SMDynamicsLab/Tappingduino/manuscript/figures/Asynch_S001_BB_alltrials.png

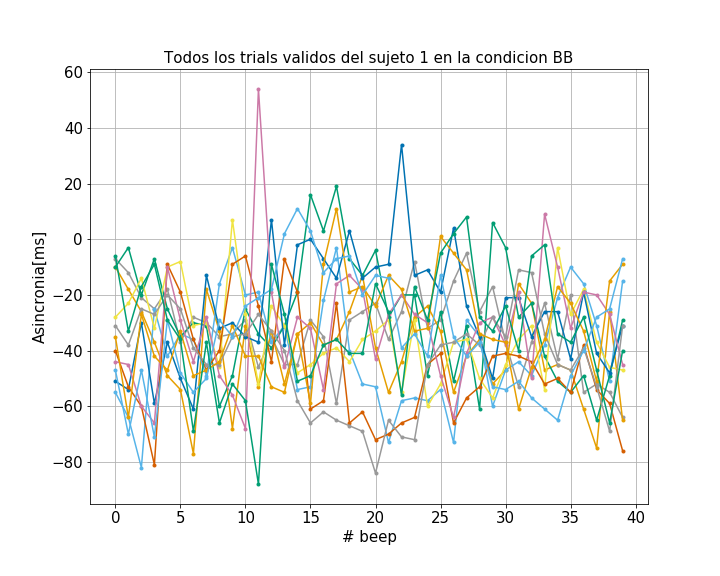
manuscript/figures/Asynch_S001_BB_alltrials.png
