SMDynamicsLab/Tappingduino/manuscript/figures/CuadroANOVA_ID.png

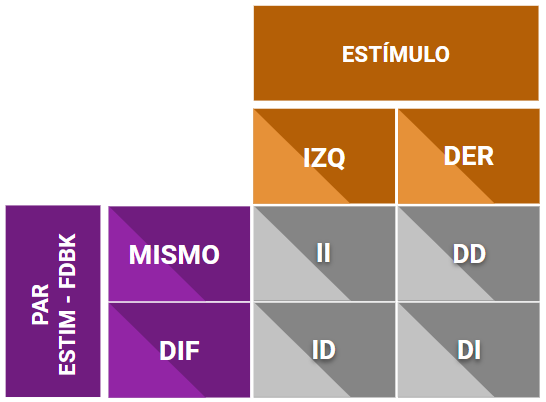
manuscript/figures/CuadroANOVA_ID.png
