SMDynamicsLab/Tappingduino/manuscript/figures/CuadroANOVA_ID_cb.png

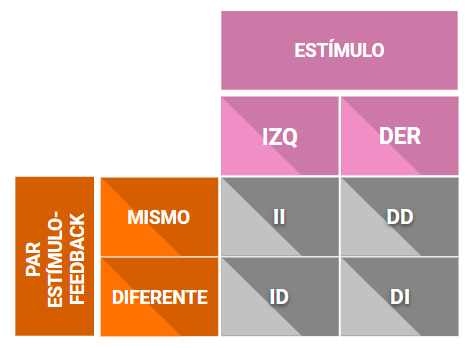
manuscript/figures/CuadroANOVA_ID_cb.png
