SMDynamicsLab/Tappingduino/manuscript/figures/CuadroStimFdbkEsp.png

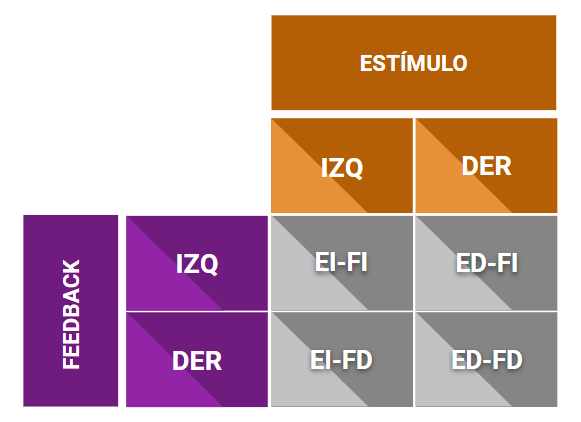
manuscript/figures/CuadroStimFdbkEsp.png
