SMDynamicsLab/Tappingduino/manuscript/figures/distrib_asinc_esquema.png

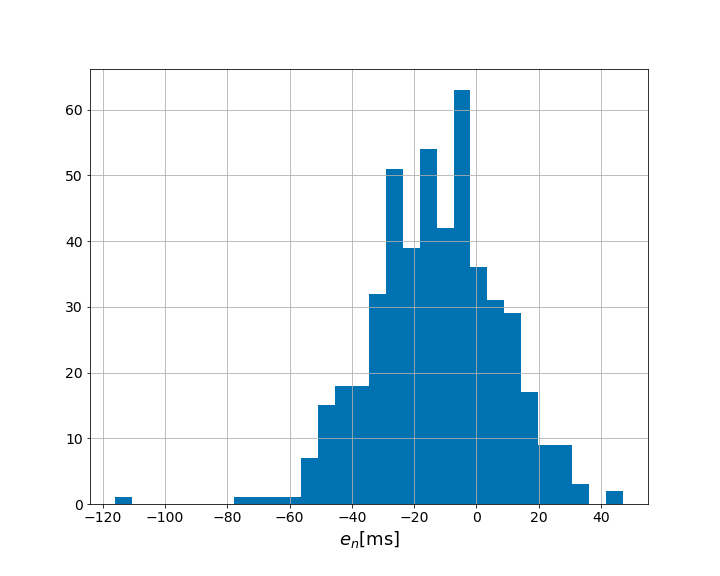
manuscript/figures/distrib_asinc_esquema.png
