SMDynamicsLab/Tappingduino/manuscript/figures/DistribAsinc_CondDD.png

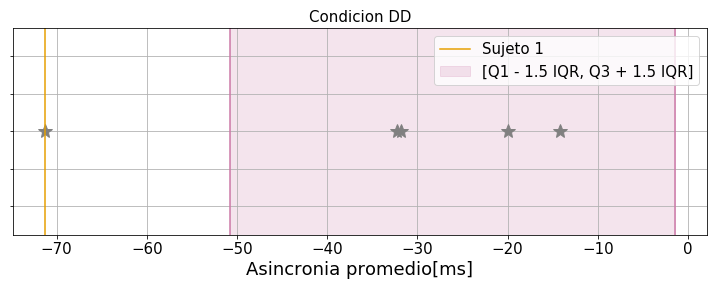
manuscript/figures/DistribAsinc_CondDD.png
