SMDynamicsLab/Tappingduino/manuscript/figures/esquema1av2.png

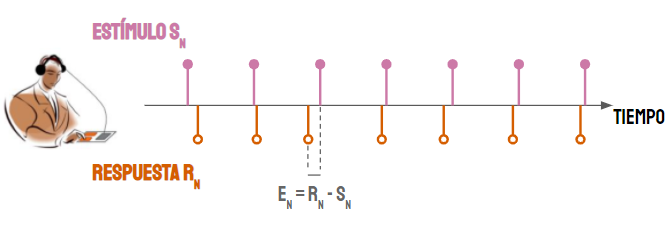
manuscript/figures/esquema1av2.png
