SMDynamicsLab/Tappingduino/manuscript/figures/esquema1b.png

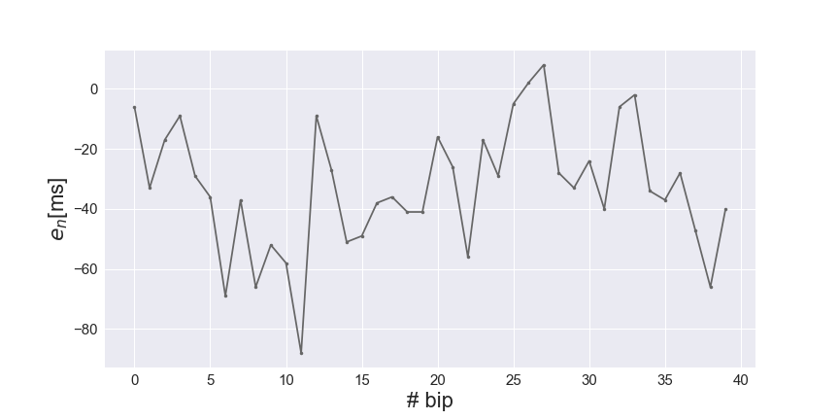
manuscript/figures/esquema1b.png
