SMDynamicsLab/Tappingduino/manuscript/figures/esquema2v2.png

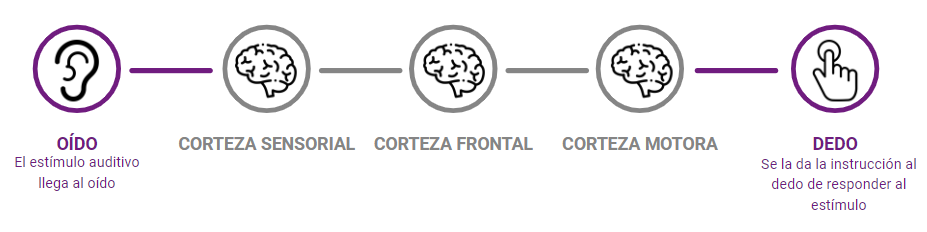
manuscript/figures/esquema2v2.png
