SMDynamicsLab/Tappingduino/manuscript/figures/esquema2v3.png

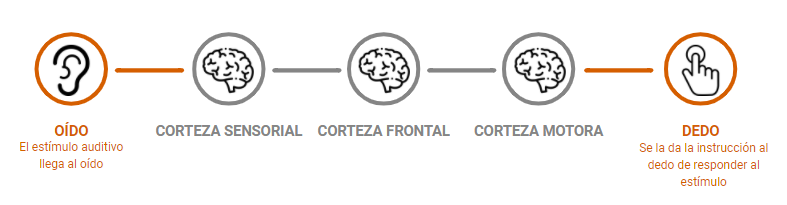
manuscript/figures/esquema2v3.png
