SMDynamicsLab/Tappingduino/manuscript/figures/esquema3v3.png

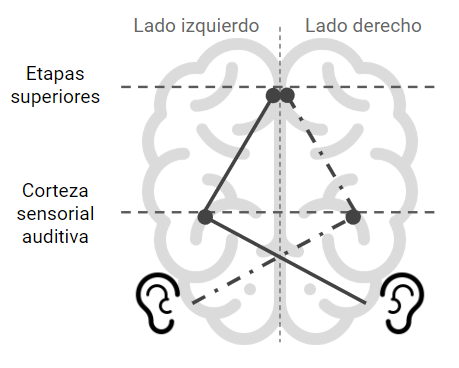
manuscript/figures/esquema3v3.png
