SMDynamicsLab/Tappingduino/manuscript/figures/esquema3v4.png

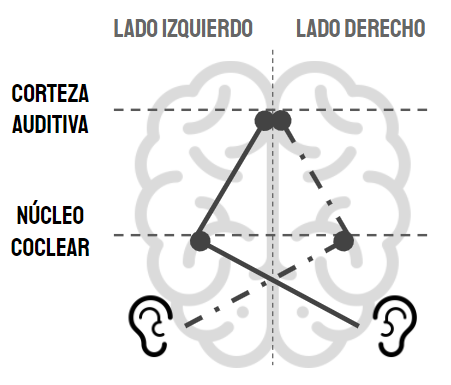
manuscript/figures/esquema3v4.png
