SMDynamicsLab/Tappingduino/manuscript/figures/esquema3v5.png

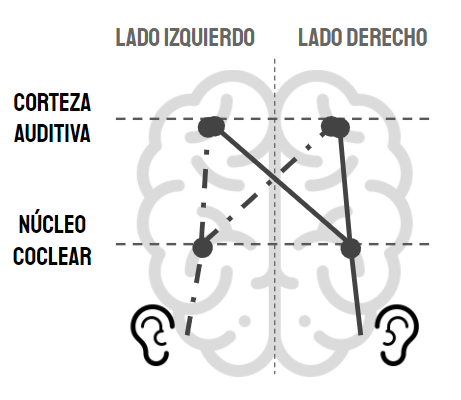
manuscript/figures/esquema3v5.png
