SMDynamicsLab/Tappingduino/manuscript/figures/esquema3v6.png

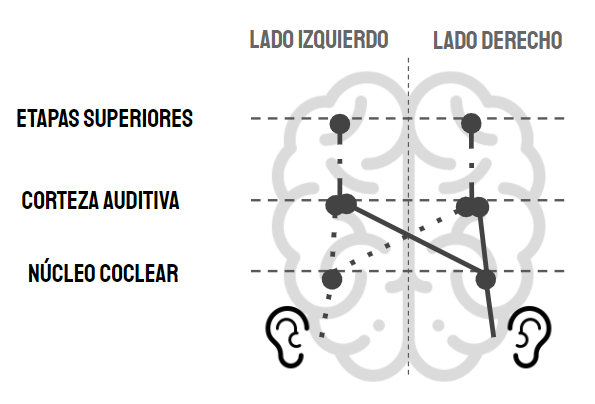
manuscript/figures/esquema3v6.png
