SMDynamicsLab/Tappingduino/manuscript/figures/esquema4av2.png

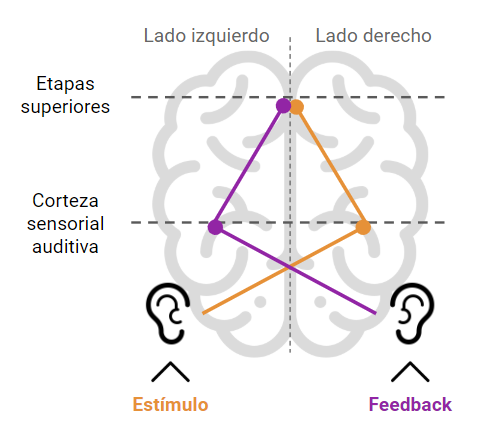
manuscript/figures/esquema4av2.png
