SMDynamicsLab/Tappingduino/manuscript/figures/esquema4bv2.png

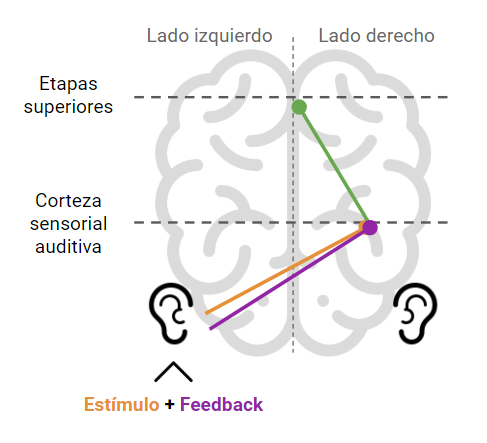
manuscript/figures/esquema4bv2.png
