SMDynamicsLab/Tappingduino/manuscript/figures/esquema4v2.png

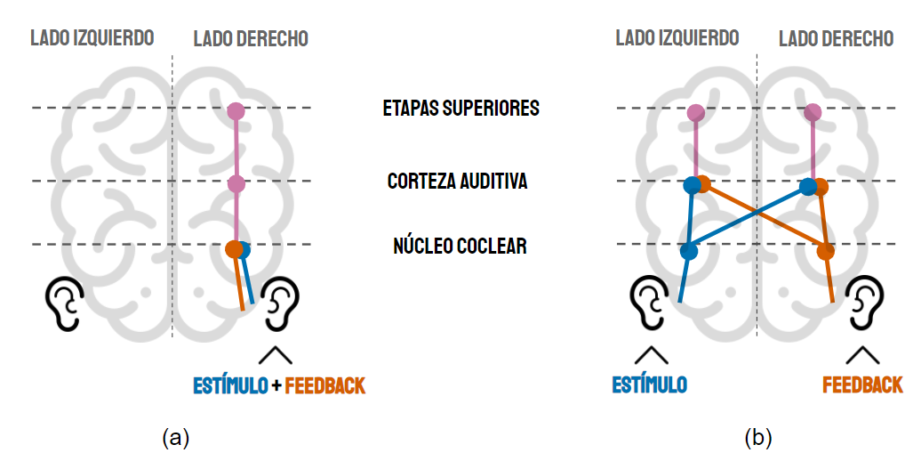
manuscript/figures/esquema4v2.png
