SMDynamicsLab/Tappingduino/manuscript/figures/Factores_nuevos_3subj_MEAN.png

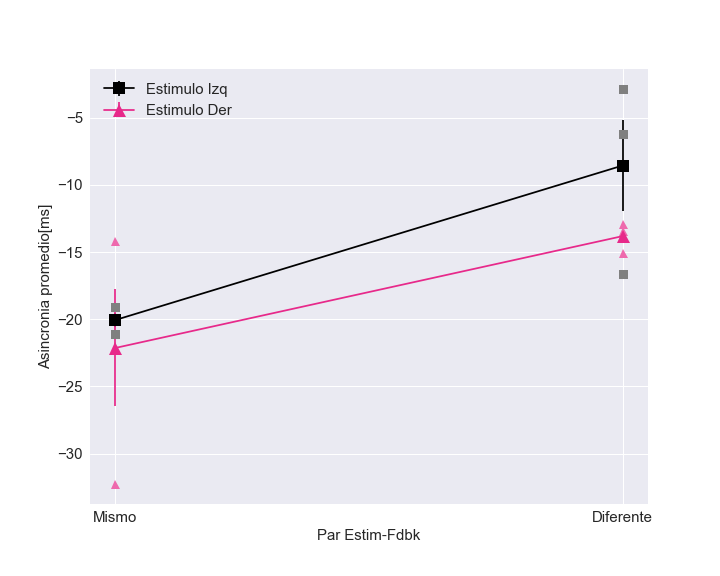
manuscript/figures/Factores_nuevos_3subj_MEAN.png
