SMDynamicsLab/Tappingduino/manuscript/figures/Factores_nuevos_3subj_STD.png

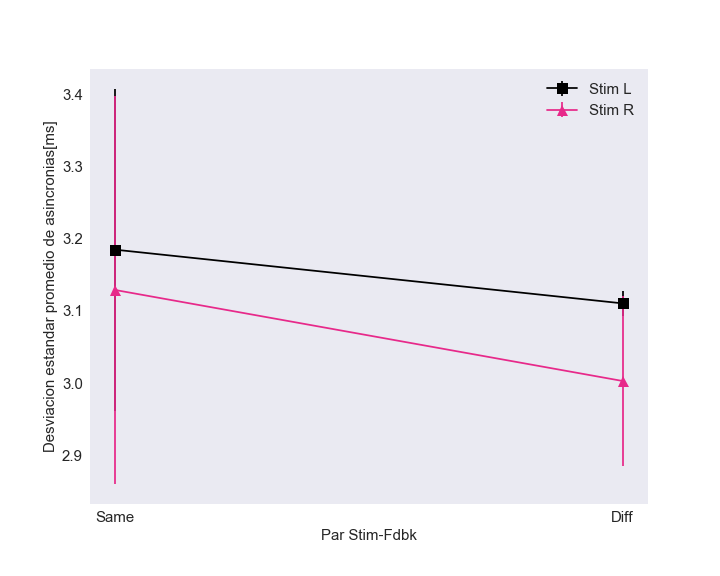
manuscript/figures/Factores_nuevos_3subj_STD.png
