SMDynamicsLab/Tappingduino/manuscript/figures/Factores_nuevos_MEAN.png

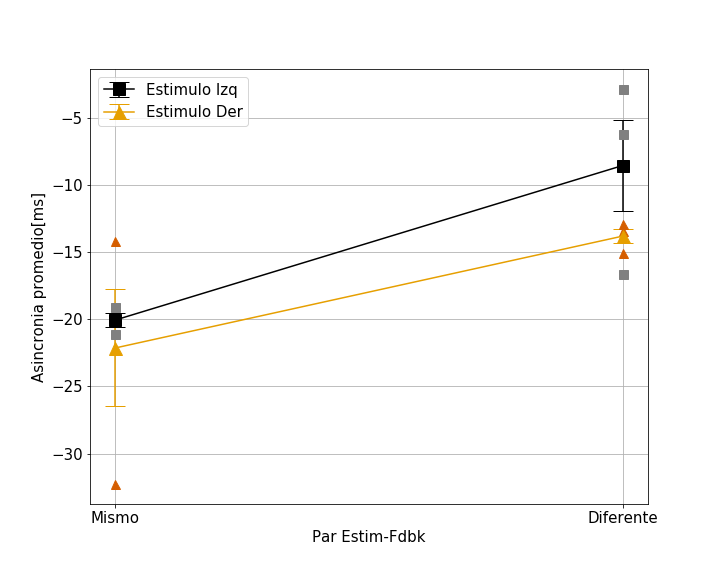
manuscript/figures/Factores_nuevos_MEAN.png
