SMDynamicsLab/Tappingduino/manuscript/figures/Factores_nuevos_STD.png

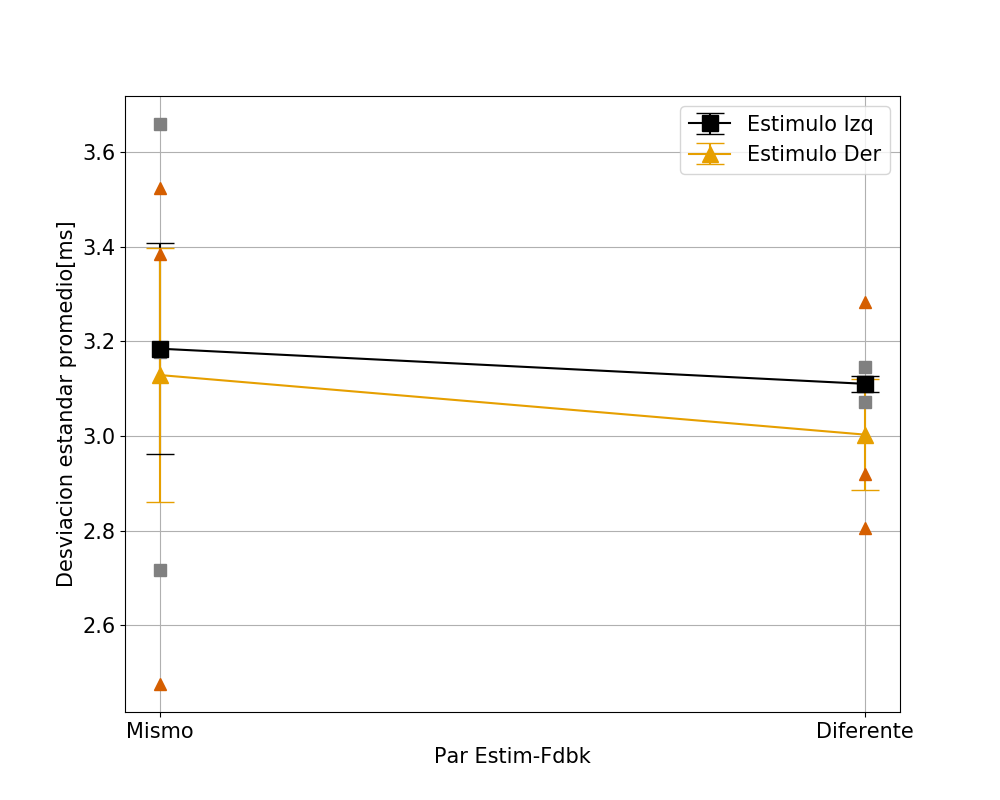
manuscript/figures/Factores_nuevos_STD.png
