SMDynamicsLab/Tappingduino/manuscript/figures/FastPWM.jpeg

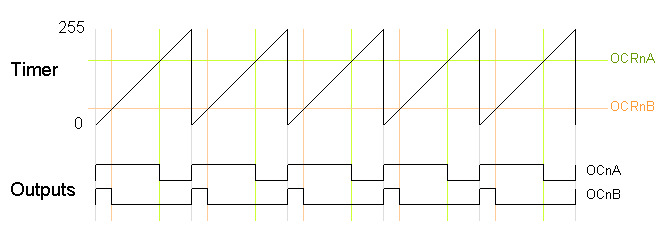
manuscript/figures/FastPWM.jpeg
