SMDynamicsLab/Tappingduino/manuscript/figures/formatodatos.png

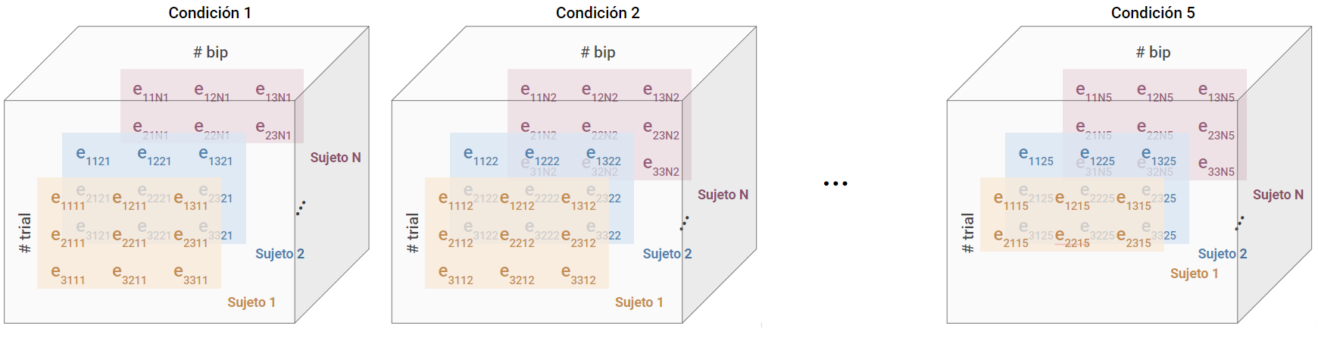
manuscript/figures/formatodatos.png
