SMDynamicsLab/Tappingduino/manuscript/figures/formatodatos_cb.png

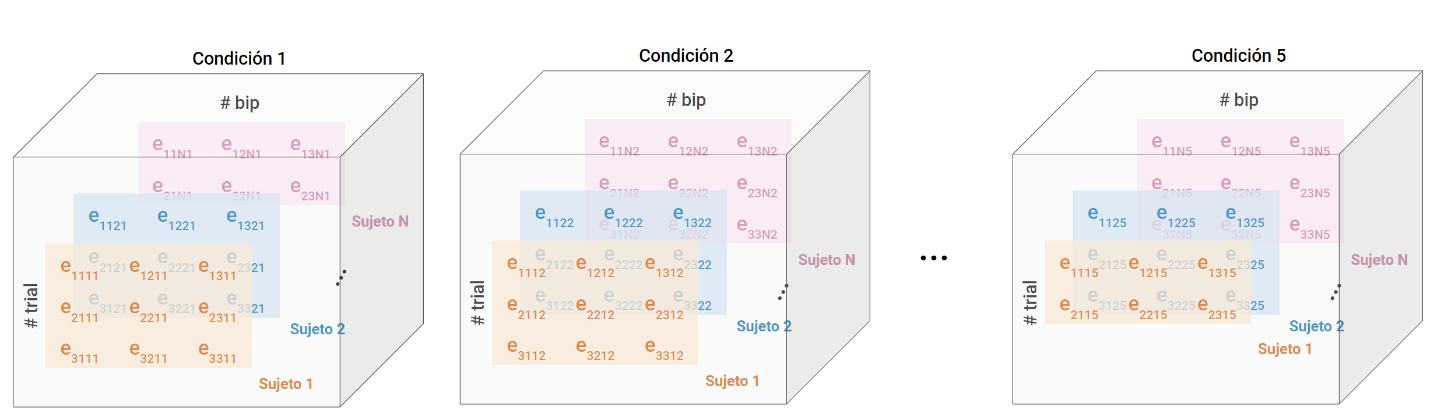
manuscript/figures/formatodatos_cb.png
