SMDynamicsLab/Tappingduino/manuscript/figures/mean_across_trials_ALLconditions.png

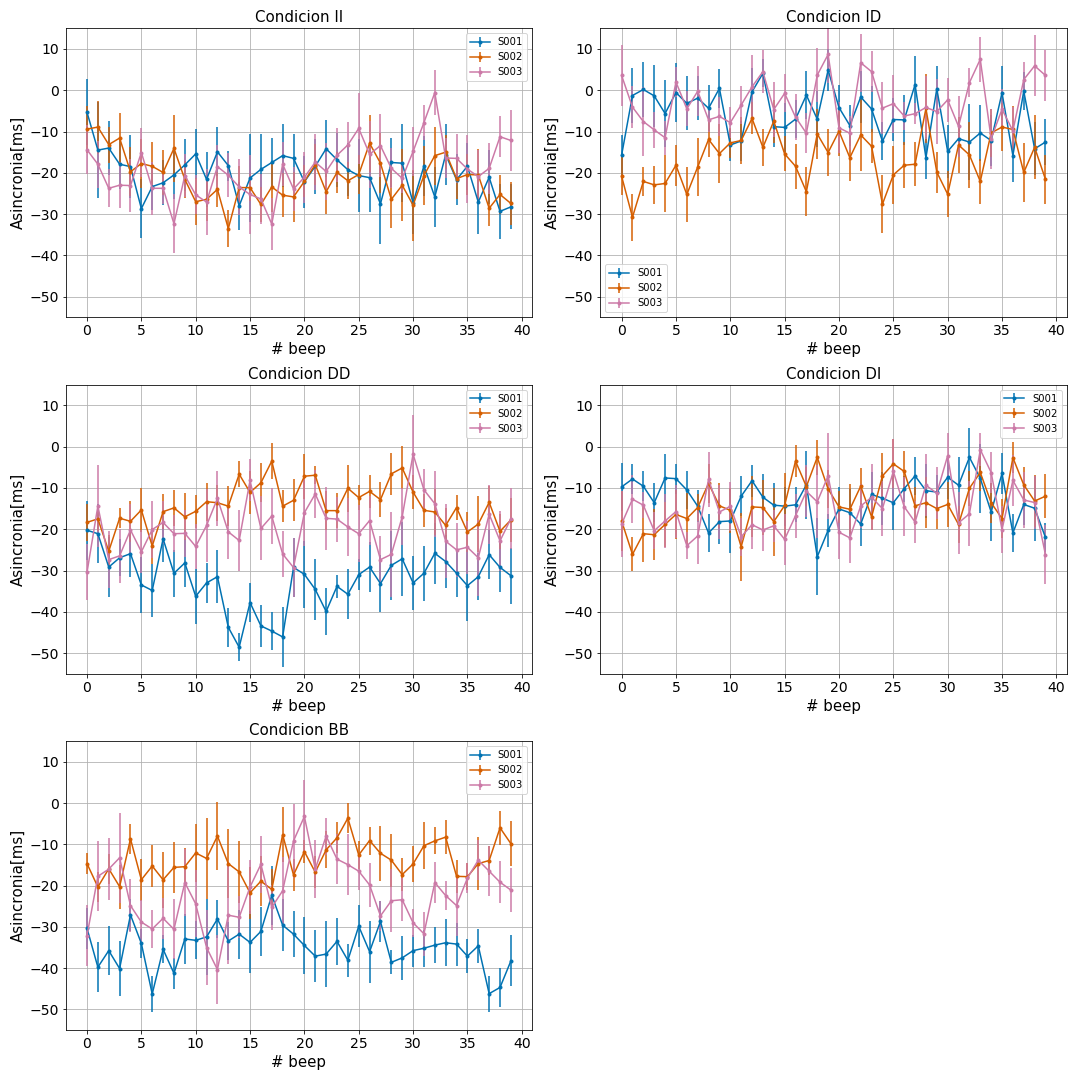
manuscript/figures/mean_across_trials_ALLconditions.png
