SMDynamicsLab/Tappingduino/manuscript/figures/mean_across_trials_BB.png

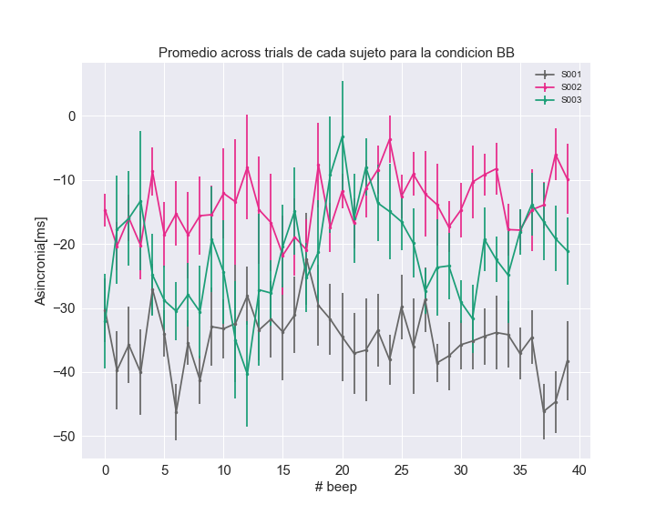
manuscript/figures/mean_across_trials_BB.png
