SMDynamicsLab/Tappingduino/manuscript/figures/mean_across_trials_LL.png

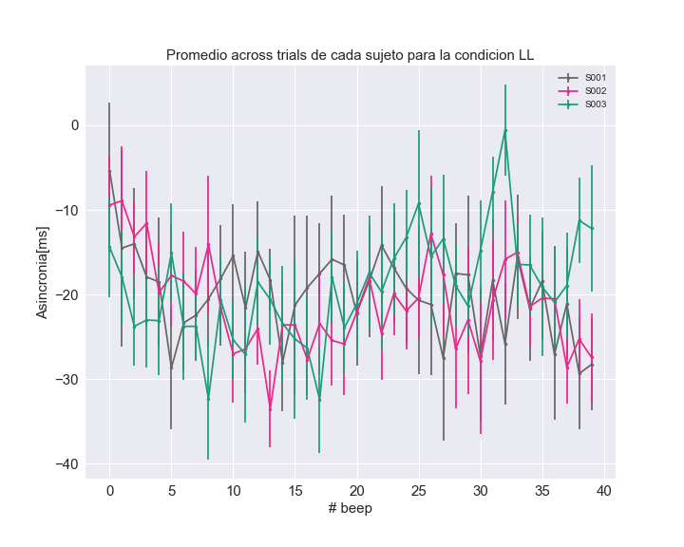
manuscript/figures/mean_across_trials_LL.png
