SMDynamicsLab/Tappingduino/manuscript/figures/mean_across_trials_RL.png

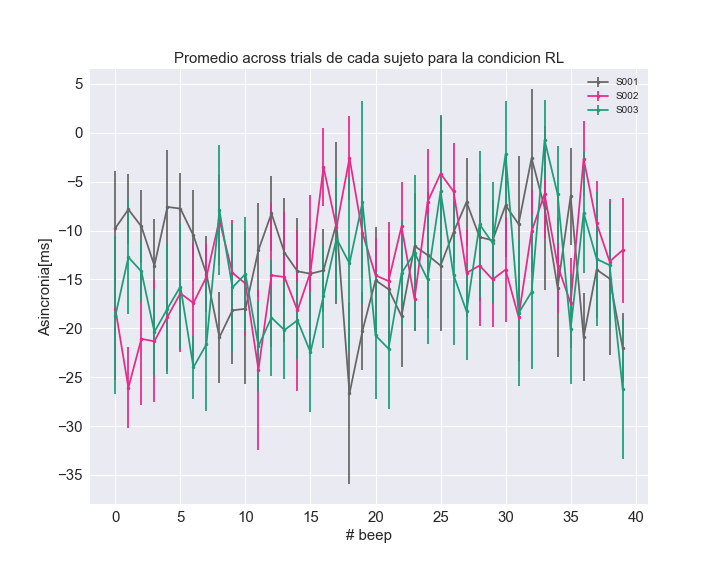
manuscript/figures/mean_across_trials_RL.png
