SMDynamicsLab/Tappingduino/manuscript/figures/mean_across_trials_RR.png

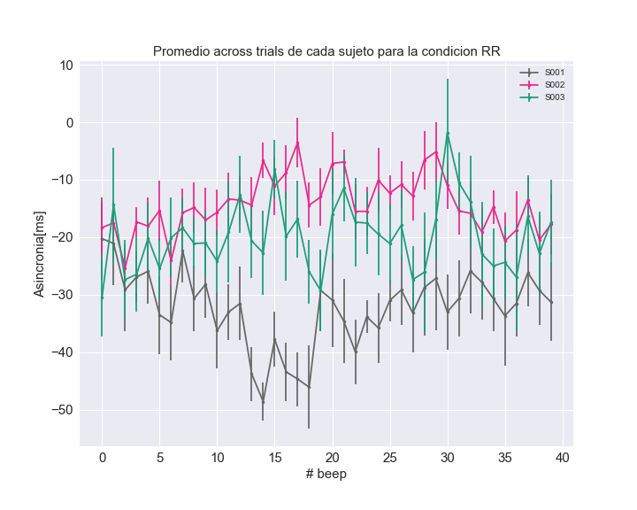
manuscript/figures/mean_across_trials_RR.png
