SMDynamicsLab/Tappingduino/manuscript/figures/Mean_Unicovalor_xSubjxCond.png

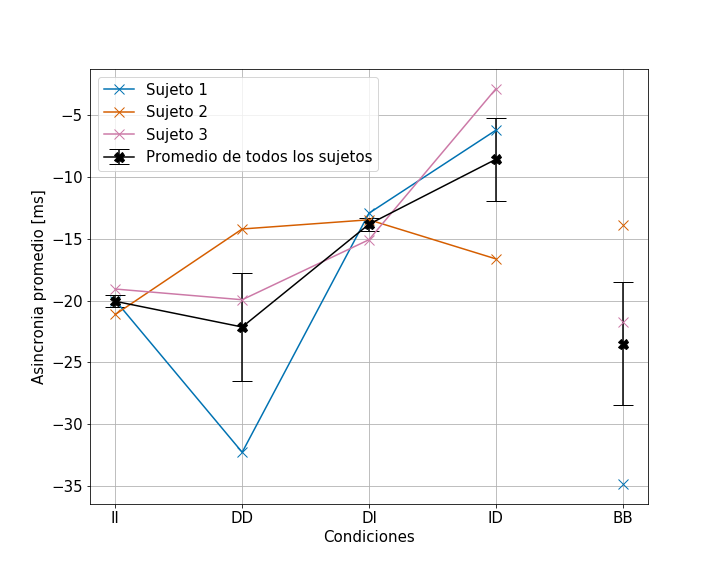
manuscript/figures/Mean_Unicovalor_xSubjxCond.png
