SMDynamicsLab/Tappingduino/manuscript/figures/Outlier_drifting.png

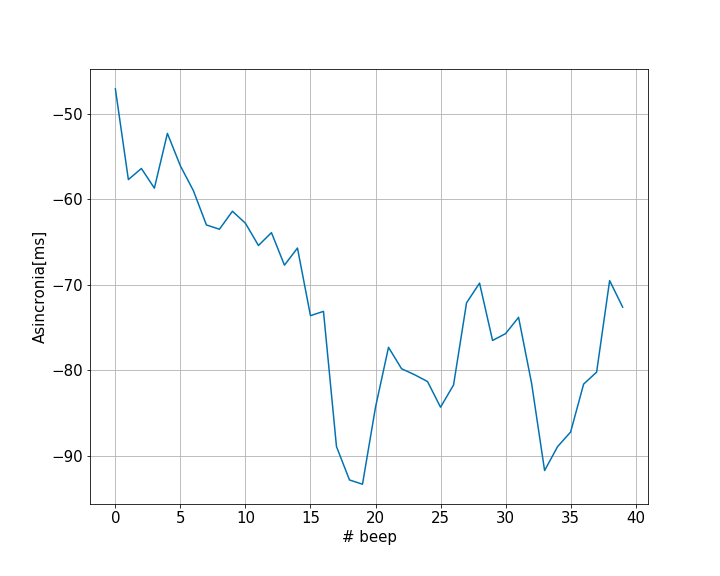
manuscript/figures/Outlier_drifting.png
