SMDynamicsLab/Tappingduino/manuscript/figures/PWMsine.jpg

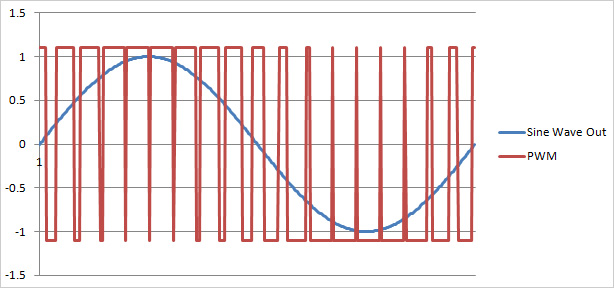
manuscript/figures/PWMsine.jpg
