SMDynamicsLab/Tappingduino/manuscript/figures/SenoCompletoy440.png

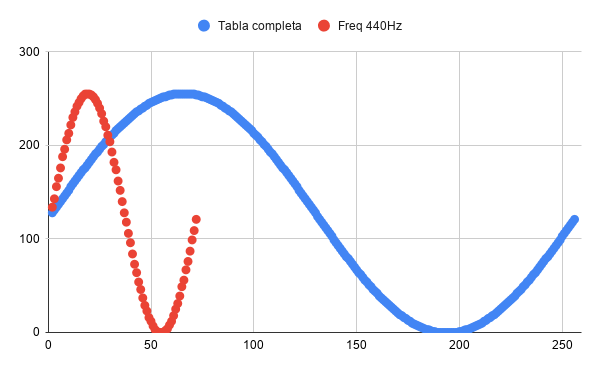
manuscript/figures/SenoCompletoy440.png
