SMDynamicsLab/Tappingduino/manuscript/figures/SingleTrial_esquema.png

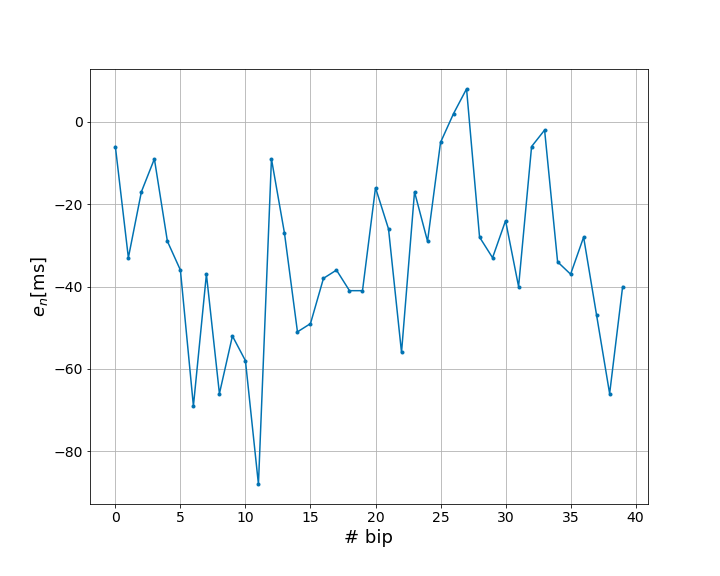
manuscript/figures/SingleTrial_esquema.png
