SMDynamicsLab/Tappingduino/manuscript/figures/Std_Unicovalor_xSubjxCond.png

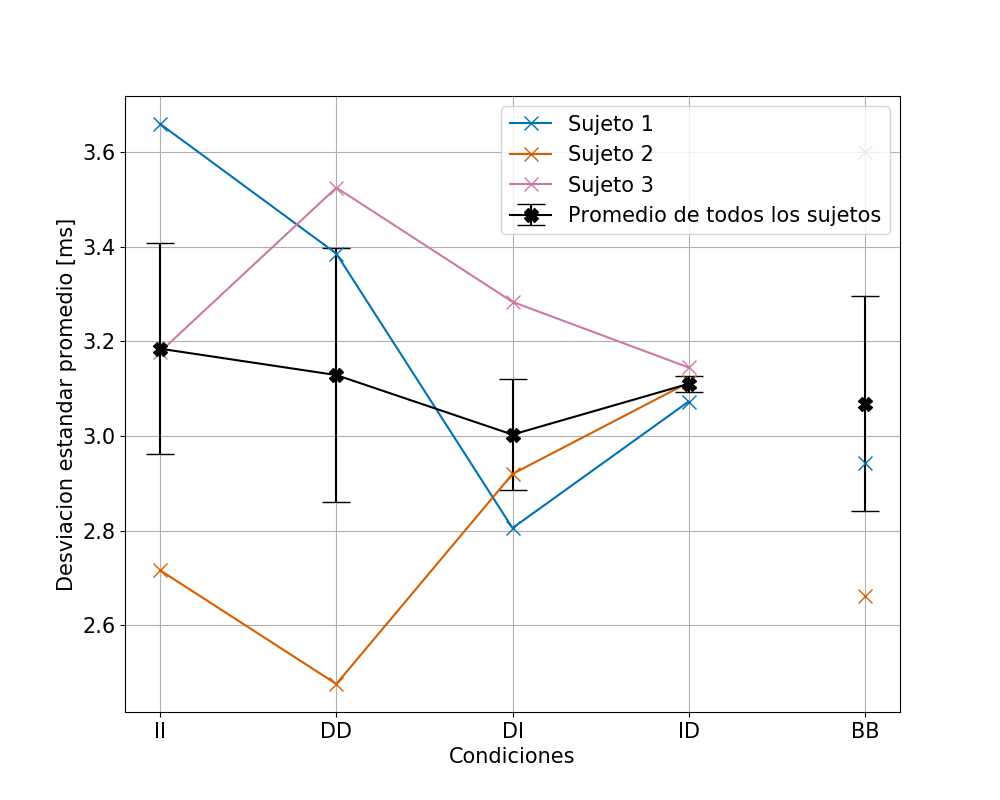
manuscript/figures/Std_Unicovalor_xSubjxCond.png
