SMDynamicsLab/Tappingduino/manuscript/figures/STD_UnicoValor_xsujetoxcond.png

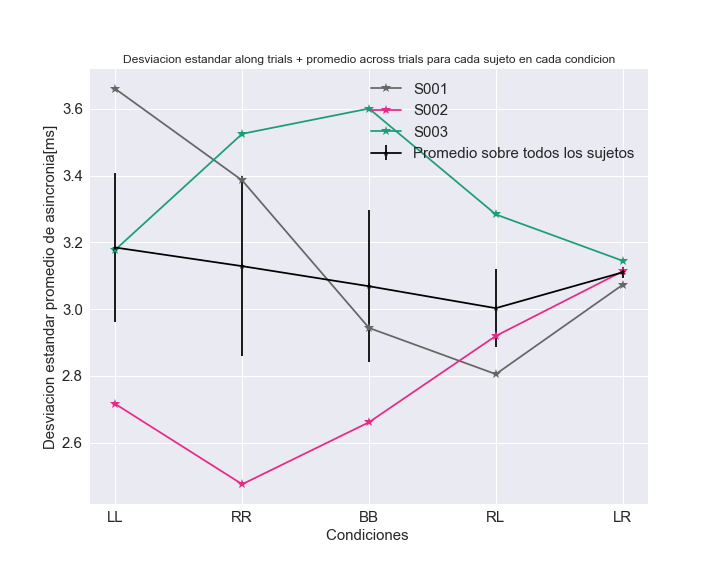
manuscript/figures/STD_UnicoValor_xsujetoxcond.png
