SMDynamicsLab/Tappingduino/manuscript/figures/TablaSineCompleta.png

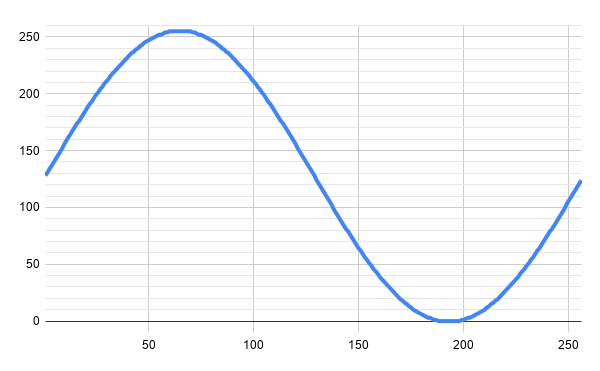
manuscript/figures/TablaSineCompleta.png
